Halogenek/modular-rf-bench/src/001-base/production-files/base-bottom.jpg

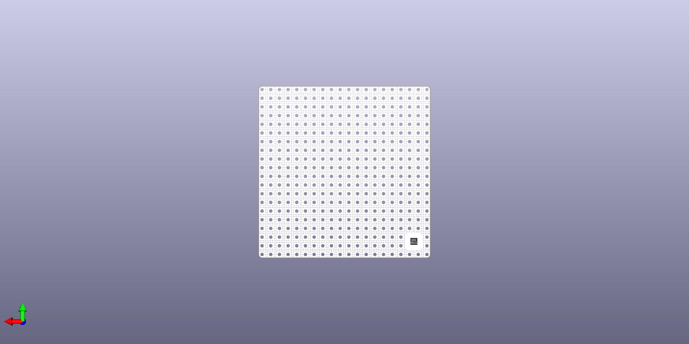
src/001-base/production-files/base-bottom.jpg
