Halogenek/modular-rf-bench/src/011-pcb-connector-castalation/production-files/pcb-connector-bottom.jpg

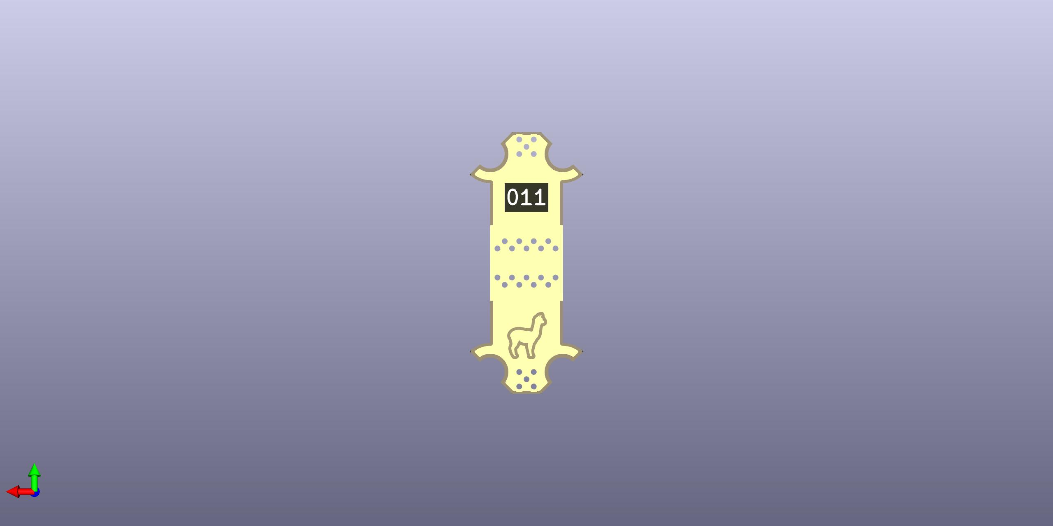
src/011-pcb-connector-castalation/production-files/pcb-connector-bottom.jpg
