Halogenek/modular-rf-bench/src/014-base-power-board/production-files/014-base-power-board-bottom.jpg

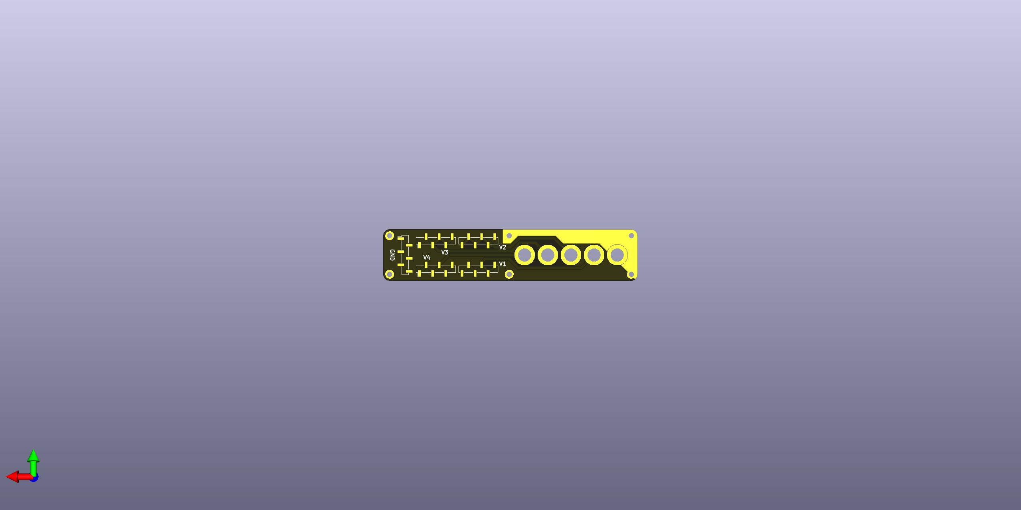
src/014-base-power-board/production-files/014-base-power-board-bottom.jpg
