Halogenek/modular-rf-bench/src/016-plastic-base-housing/production-files/016-plastic-base-housing.png

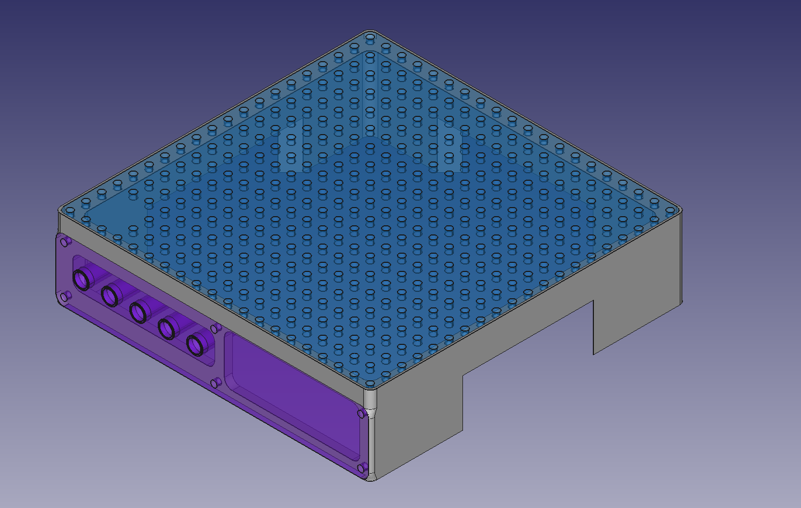
src/016-plastic-base-housing/production-files/016-plastic-base-housing.png
