Halogenek/modular-rf-bench/src/017-johnson-counter/production-files/top.jpg

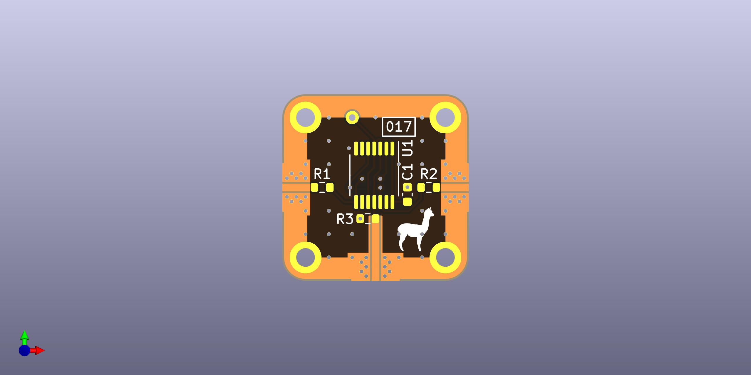
src/017-johnson-counter/production-files/top.jpg
