Halogenek/modular-rf-bench/src/019-tayloe-quadrature-product-detector/production-files/top.jpg

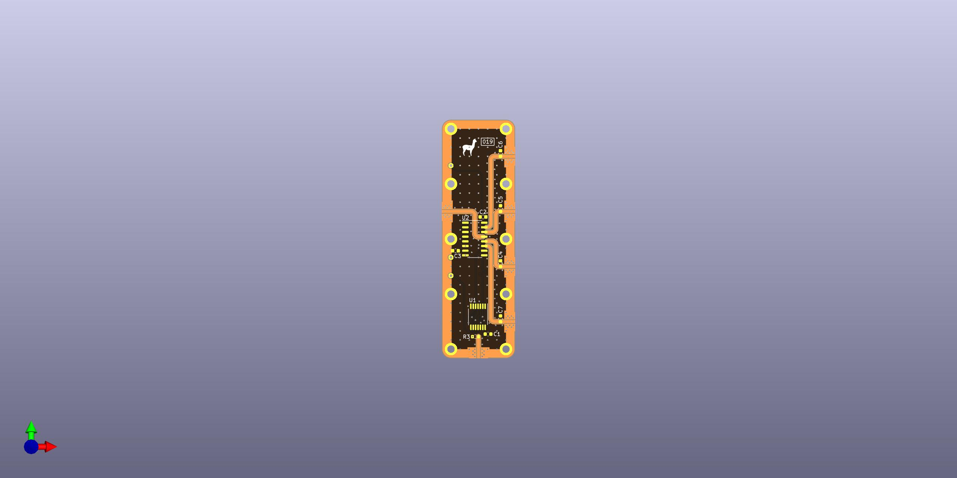
src/019-tayloe-quadrature-product-detector/production-files/top.jpg
