Halogenek/modular-rf-bench/src/bjt-amp/bjt-amp.kicad_pcb

## KiCad design src/bjt-amp/bjt-amp.kicad_pcb (2022-01-22)

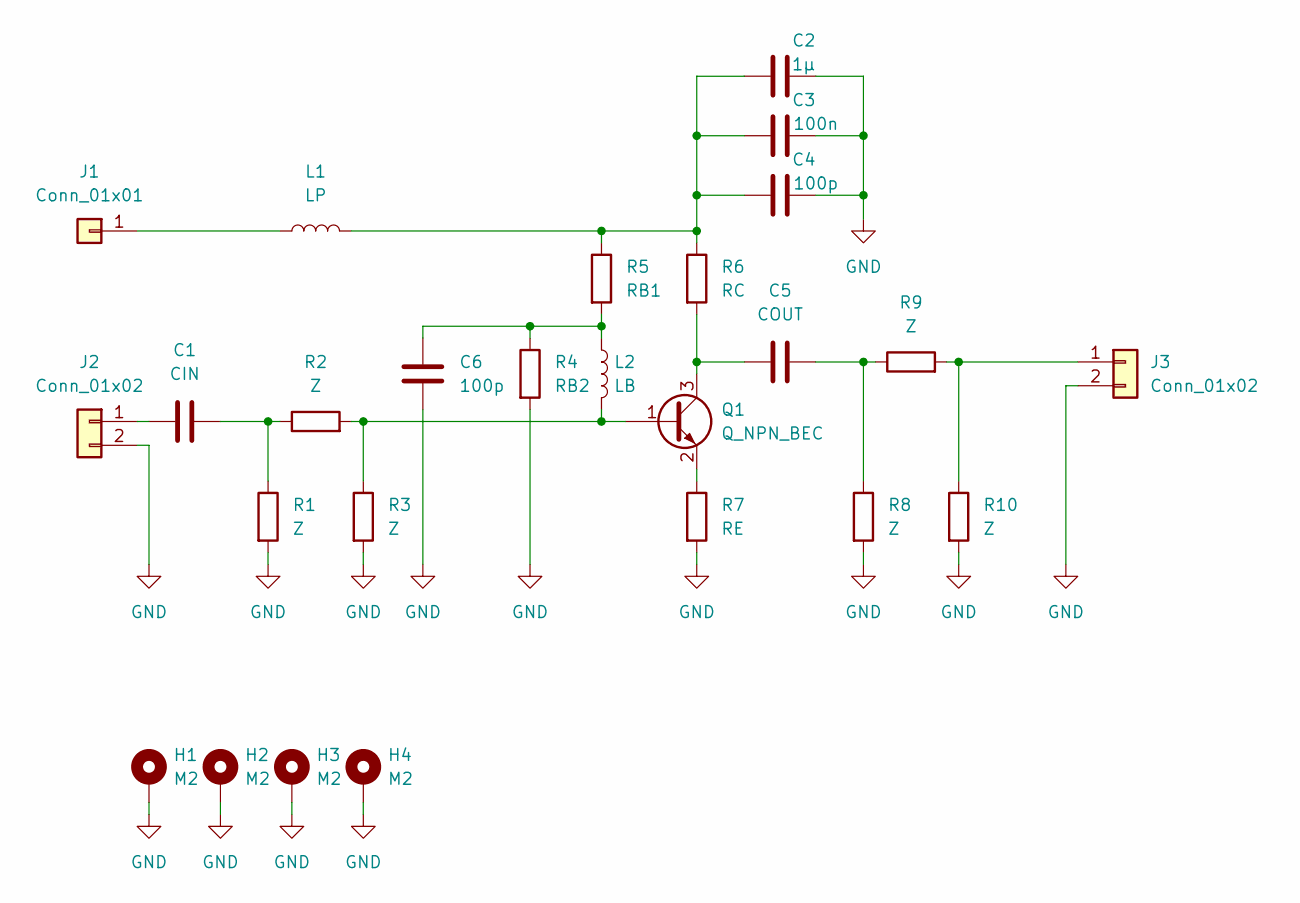
[picture p42: schematic bjt-amp.kicad_sch]

Parts:
C1: CIN; C_0603_1608Metric
C2: 1µ; C_0603_1608Metric
C3: 100n; C_0603_1608Metric
C4, C6: 100p; C_0603_1608Metric
C5: COUT; C_0603_1608Metric
H1, H2, H3, H4: M2; M2-hole
J1: Conn_01x01; SolderWire-0.25sqmm_1x01_D0.65mm_OD1.7mm
J2, J3: Conn_01x02; edge-connector
L1: LP; L_0603_1608Metric
L2: LB; L_0603_1608Metric
Q1: Q_NPN_BEC; SOT-23
R1, R2, R3, R8, R9, R10: Z; R_0603_1608Metric
R4: RB2; R_0603_1608Metric
R5: RB1; R_0603_1608Metric
R6: RC; R_0603_1608Metric
R7: RE; R_0603_1608Metric

Connections:
GND: C2.2, C3.2, C4.2, C6.1, H1.1, H2.1, H3.1, H4.1, J2.2, J3.2, R1.2, R3.2, R4.2, R7.2, R8.2, R10.2
unnamed: C1.1, J2.1
unnamed: C1.2, R1.1, R2.1
unnamed: C2.1, C3.1, C4.1, L1.2, R5.1, R6.1
unnamed: C5.1, Q1.3 (C), R6.2
unnamed: C5.2, R8.1, R9.1
unnamed: C6.2, L2.1, R4.1, R5.2
unnamed: J1.1, L1.1
unnamed: J3.1, R9.2, R10.1
unnamed: L2.2, Q1.1 (B), R2.2, R3.1
unnamed: Q1.2 (E), R7.1

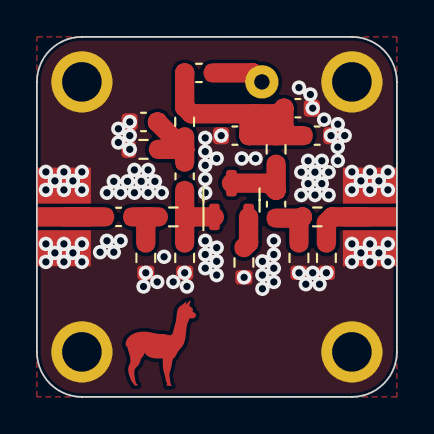
[picture p43: board bjt-amp.kicad_pcb from above]

Board: 2 copper layers, 20.0 x 20.0 mm, 26 parts (0 on the bottom side), 11 nets.
